boaschti/MQTT_Node_RFM69/Board V2.0/maxi Node/Layout.JPG

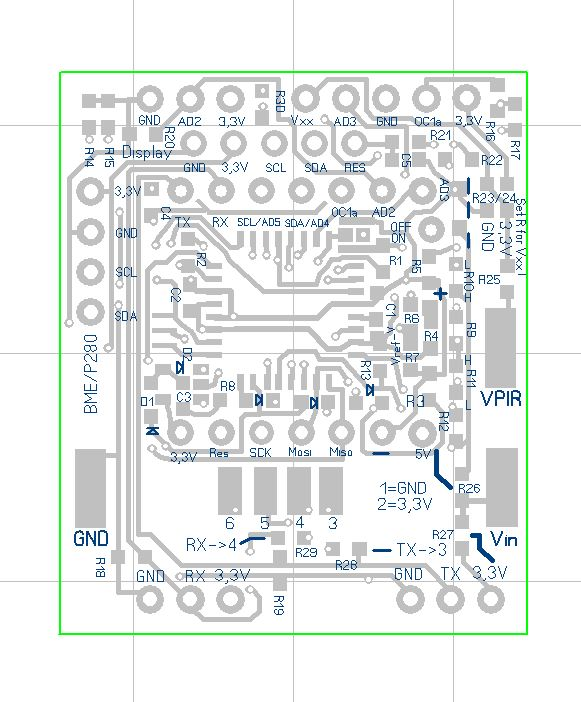
Board V2.0/maxi Node/Layout.JPG
