boaschti/MQTT_Node_RFM69/Board V2.0/mini Node/platine rfm12b 2.0 version12V.JPG

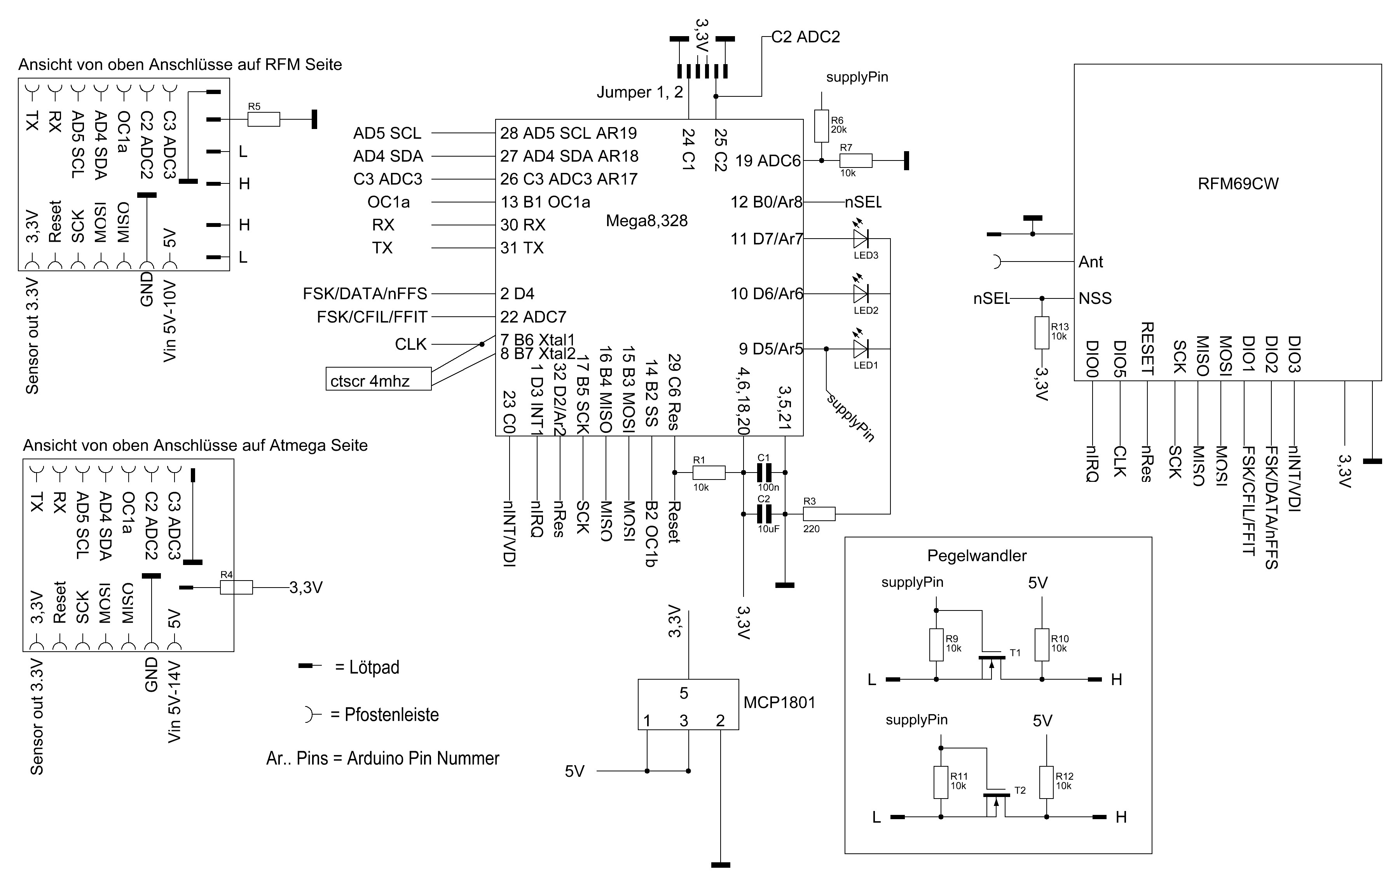
Board V2.0/mini Node/platine rfm12b 2.0 version12V.JPG
