boaschti/MQTT_Node_RFM69/Board V2.0/mini Node/RS232FunkV2.0kpl.JPG

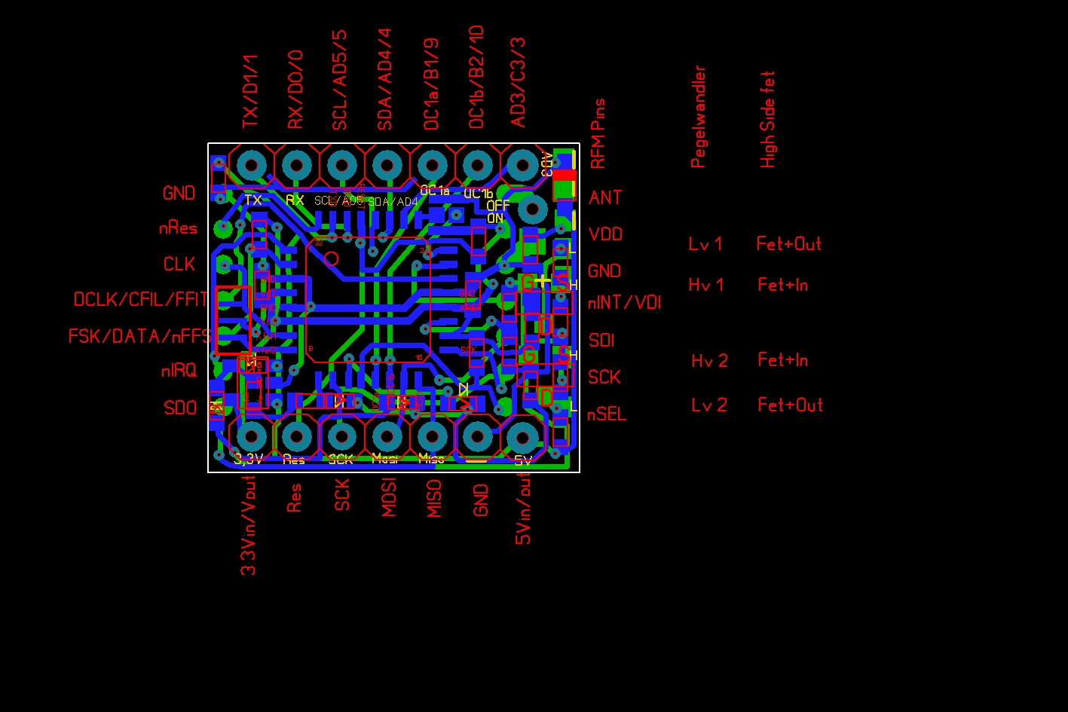
Board V2.0/mini Node/RS232FunkV2.0kpl.JPG
