boaschti/MQTT_Node_RFM69/pictures/3AAA_pir_node_inside.jpg

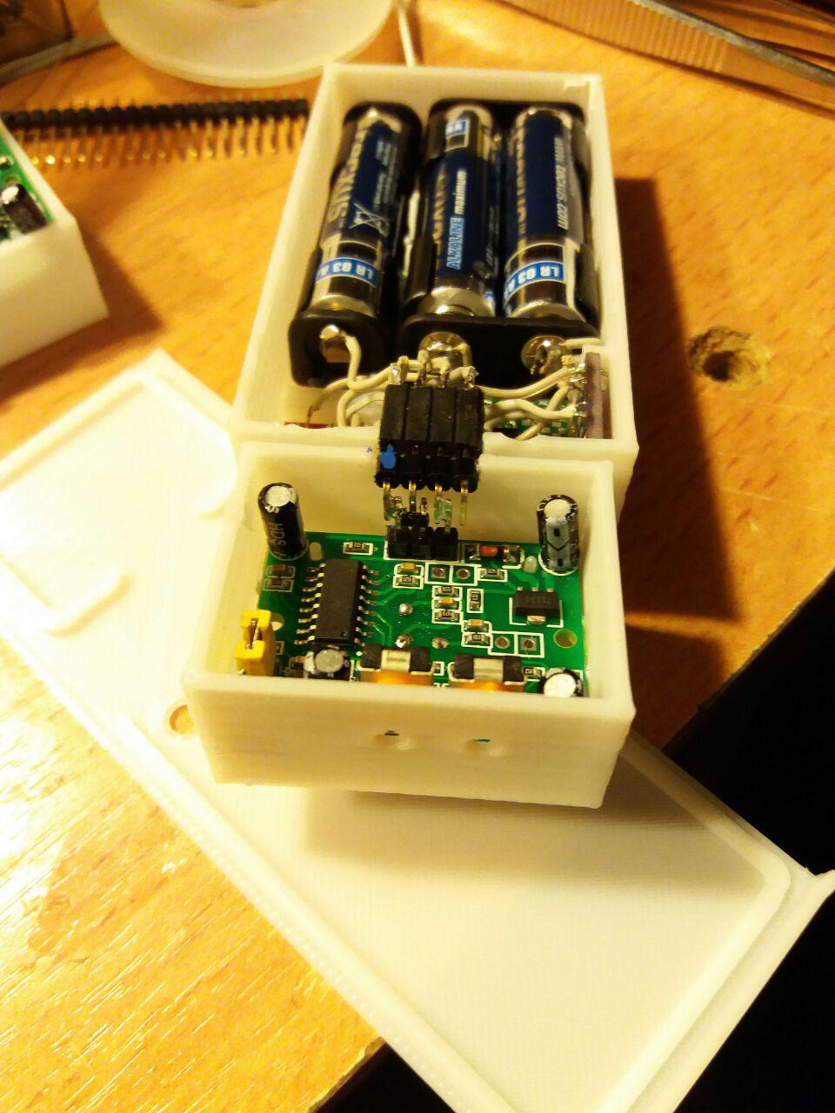
pictures/3AAA_pir_node_inside.jpg
