boaschti/MQTT_Node_RFM69/pictures/pirHousing.jpg

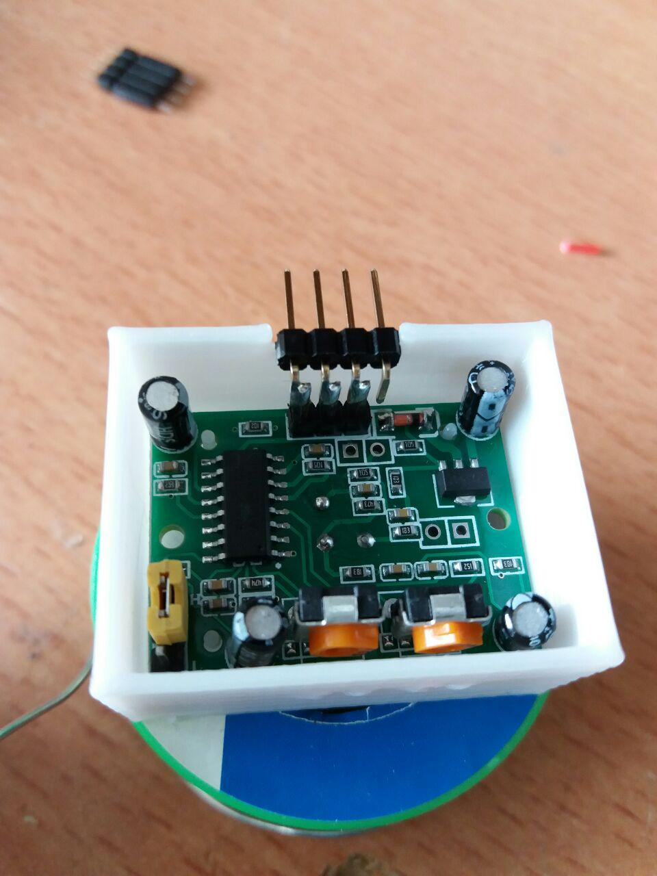
pictures/pirHousing.jpg
