boaschti/MQTT_Node_RFM69/Housing/Gehause Display.FCStd

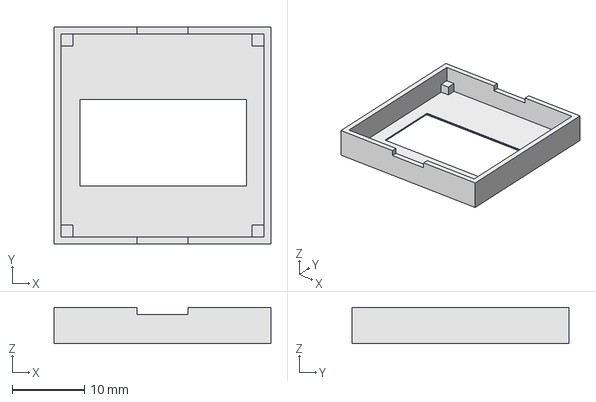
[picture p40: CAD file, 2017-03-26]
Housing/Gehause Display.FCStd
30.0 x 30.0 x 5.00 mm
