boaschti/MQTT_Node_RFM69/Housing/Deckel Node2.FCStd

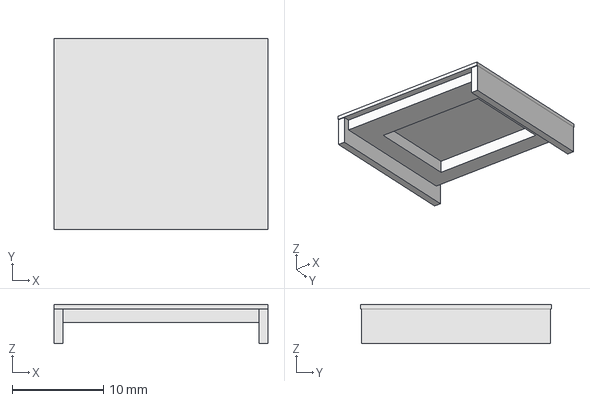
[picture p41: CAD file, 2017-03-26]
Housing/Deckel Node2.FCStd
23.5 x 21.0 x 4.30 mm
