boaschti/MQTT_Node_RFM69/Housing/Deckel Display.FCStd

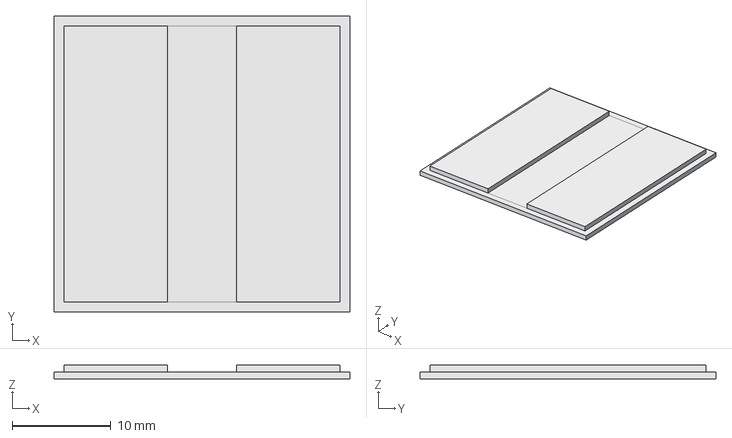
[picture p42: CAD file, 2017-03-26]
Housing/Deckel Display.FCStd
30.0 x 30.0 x 1.40 mm
