boaschti/MQTT_Node_RFM69/Housing/Gehause Node1.FCStd

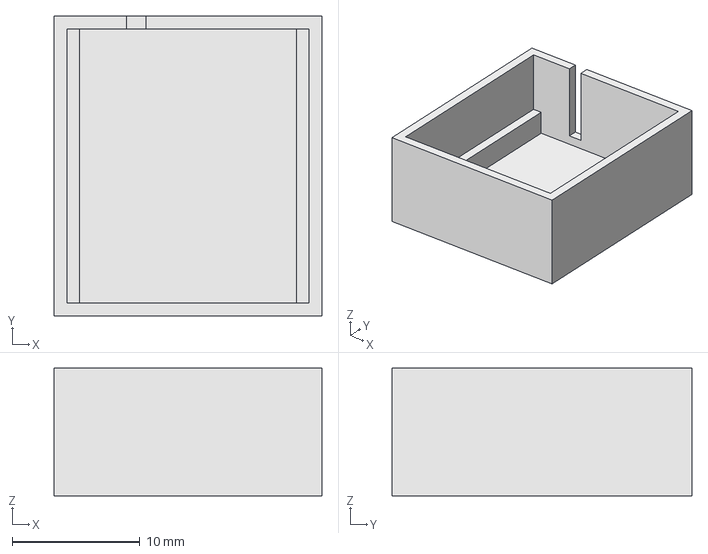
[picture p43: CAD file, 2017-03-26]
Housing/Gehause Node1.FCStd
21.0 x 23.5 x 10.0 mm
