boaschti/MQTT_Node_RFM69/Housing/Deckel Node1.FCStd

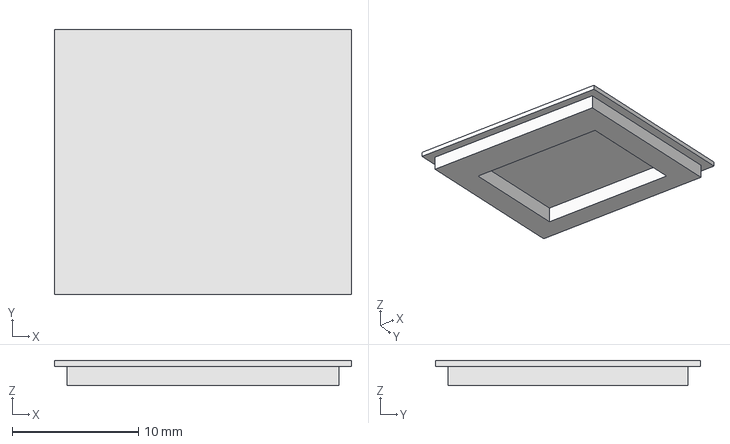
[picture p44: CAD file, 2017-03-26]
Housing/Deckel Node1.FCStd
23.5 x 21.0 x 2.00 mm
